Bjack795/WemosD32pro_EPD_Typewriter/Case/Cerniera/Cerniera 2.stl

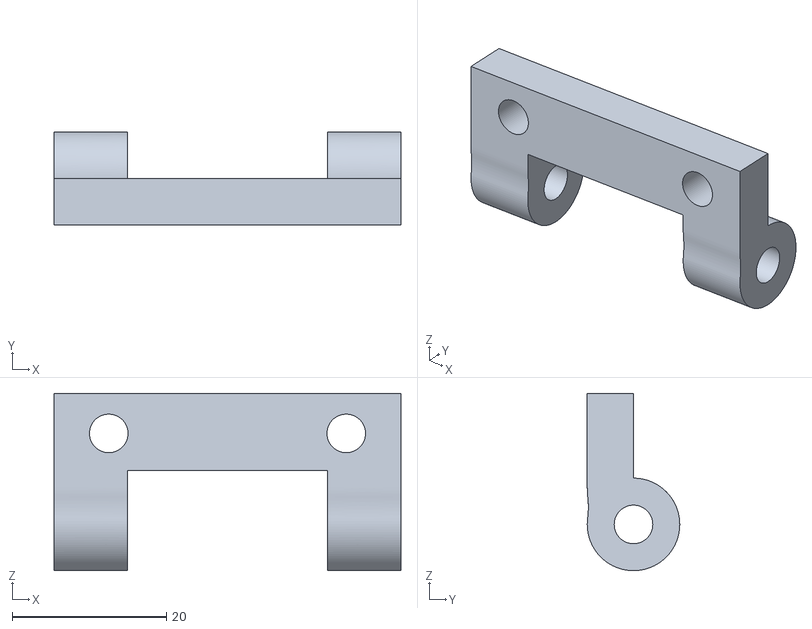
[picture p16: CAD file, 2019-07-26]
Case/Cerniera/Cerniera 2.stl
45.0 x 12.0 x 23.0
