Bjack795/WemosD32pro_EPD_Typewriter/Case/Cerniera/Definitiva/Cerniera_cov.stl

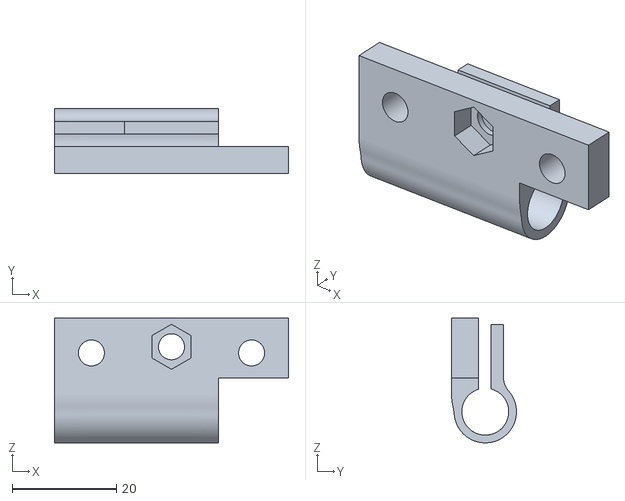
[picture p17: CAD file, 2019-07-26]
Case/Cerniera/Definitiva/Cerniera_cov.stl
45.0 x 12.5 x 24.0
