Bjack795/WemosD32pro_EPD_Typewriter/Case/Cerniera/Versione 3/Cerniera 5.5.stl

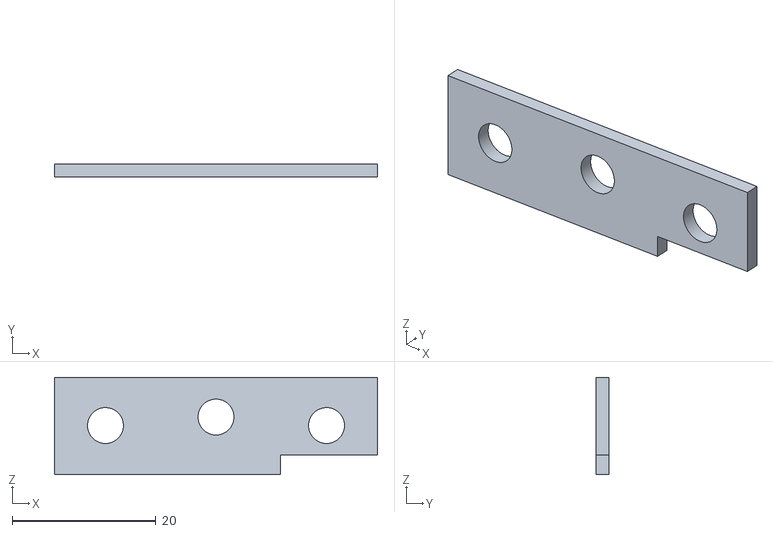
[picture p18: CAD file, 2019-07-26]
Case/Cerniera/Versione 3/Cerniera 5.5.stl
45.0 x 1.84 x 13.5
