Bjack795/WemosD32pro_EPD_Typewriter/Case/Case 3Dprinted/A/Case_A1.stl

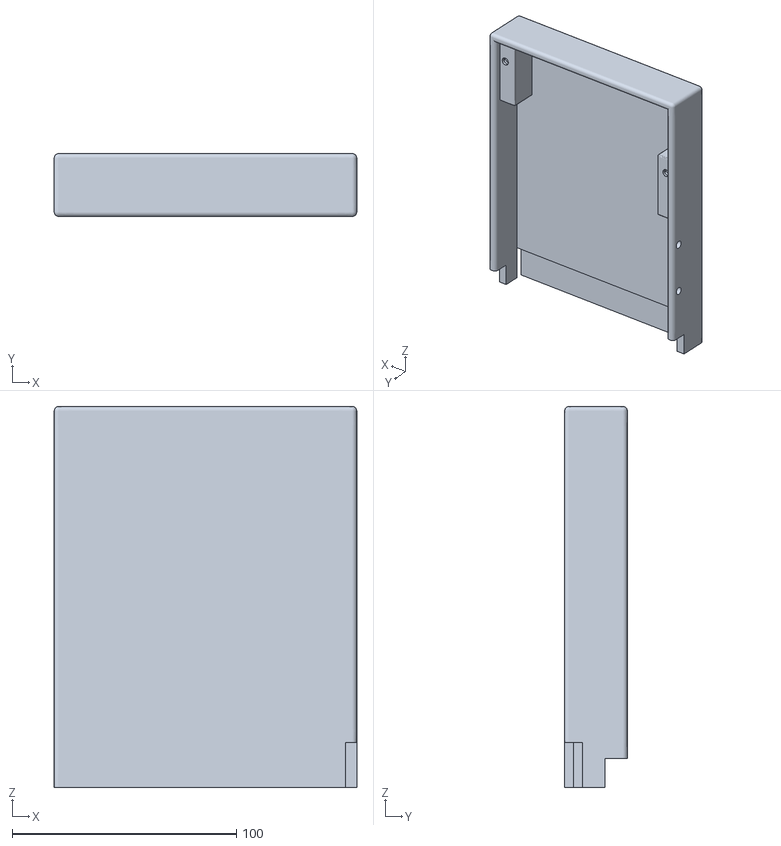
[picture p19: CAD file, 2019-07-26]
Case/Case 3Dprinted/A/Case_A1.stl
135.0 x 28.0 x 170.0
