Bjack795/WemosD32pro_EPD_Typewriter/Case/Case 3Dprinted/B/CE3_Case_B1.3mf

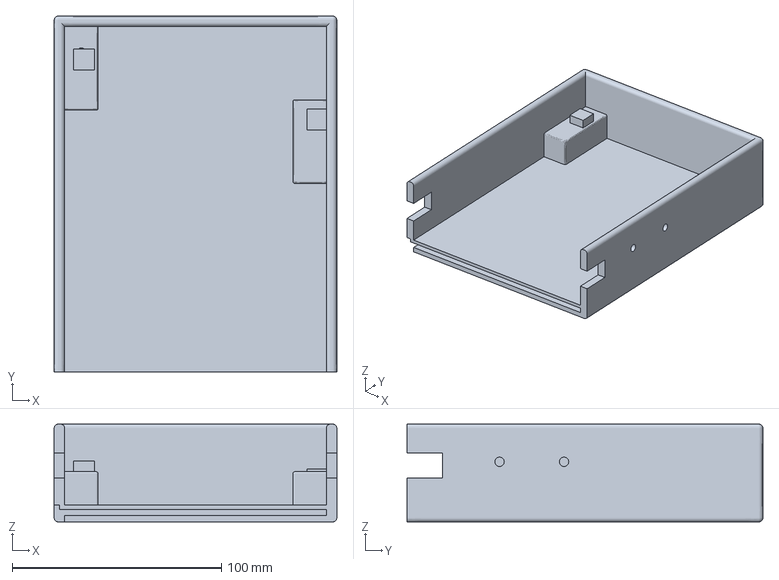
[picture p20: CAD file, 2019-07-26]
Case/Case 3Dprinted/B/CE3_Case_B1.3mf
135.0 x 170.0 x 46.7 mm
