Bjack795/WemosD32pro_EPD_Typewriter/Case/Case 3Dprinted/Placca B/PlaccaB_1.stl

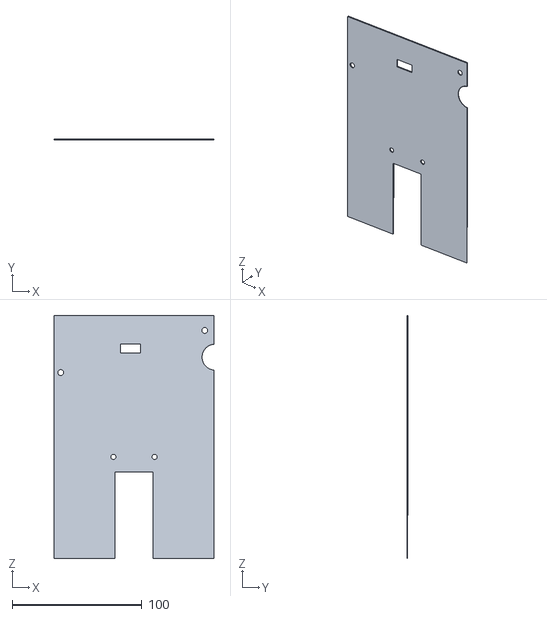
[picture p21: CAD file, 2019-08-01]
Case/Case 3Dprinted/Placca B/PlaccaB_1.stl
123.0 x 1.00 x 187.3
