Bjack795/WemosD32pro_EPD_Typewriter/Case/Case 3Dprinted/Placchetta/Placchetta.stl

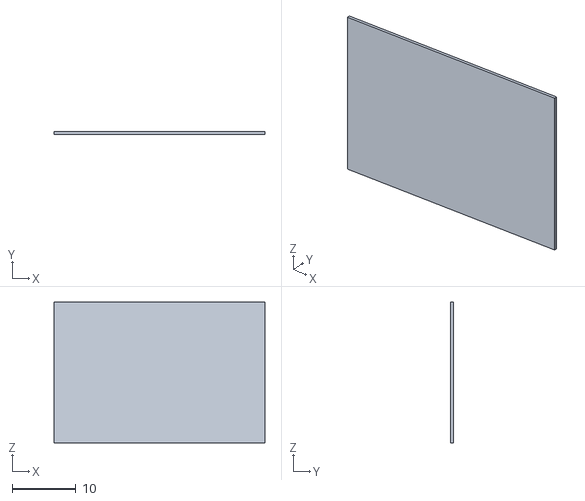
[picture p22: CAD file, 2019-08-01]
Case/Case 3Dprinted/Placchetta/Placchetta.stl
33.0 x 0.4 x 22.0
