Bjack795/WemosD32pro_EPD_Typewriter/Case/Cerniera/CE3_Cerniera.3mf

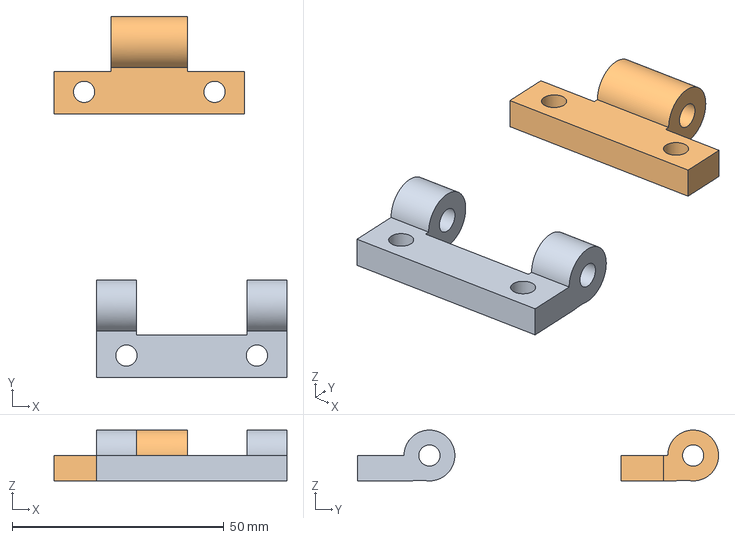
[picture p23: CAD file, 2019-07-26]
Case/Cerniera/CE3_Cerniera.3mf
55.0 x 85.2 x 12.0 mm
