Bjack795/WemosD32pro_EPD_Typewriter/Case/Cerniera/Definitiva/Cerniera_definitiva.3mf

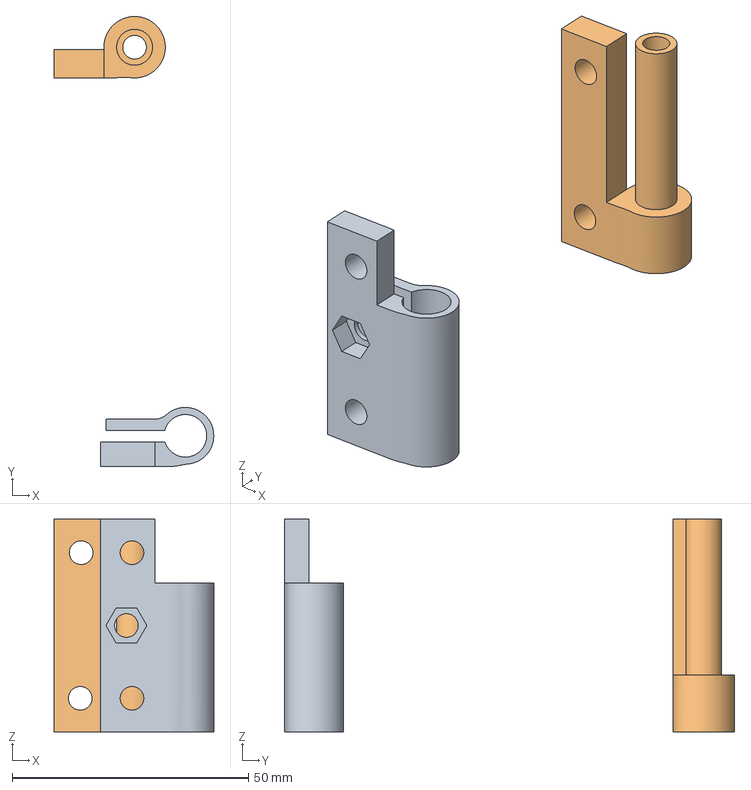
[picture p24: CAD file, 2019-07-26]
Case/Cerniera/Definitiva/Cerniera_definitiva.3mf
33.8 x 95.2 x 45.0 mm
