Bjack795/WemosD32pro_EPD_Typewriter/Case/Cerniera/Versione 3/Cerniera_Versione 3.3mf

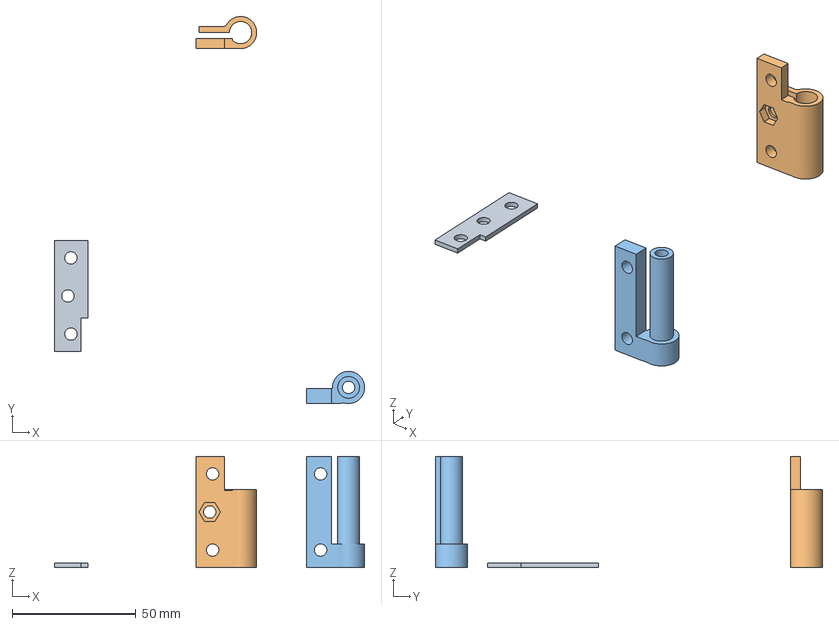
[picture p25: CAD file, 2019-07-26]
Case/Cerniera/Versione 3/Cerniera_Versione 3.3mf
125.5 x 156.5 x 45.0 mm
