Bjack795/WemosD32pro_EPD_Typewriter/Case/Case 3Dprinted/A/CE3_Case_A2.3mf

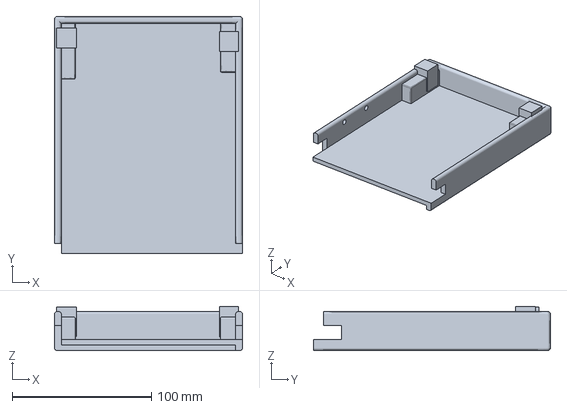
[picture p26: CAD file, 2019-07-26]
Case/Case 3Dprinted/A/CE3_Case_A2.3mf
135.0 x 170.0 x 31.6 mm
