Bjack795/WemosD32pro_EPD_Typewriter/Case/Case 3Dprinted/Prove/CE3_Prova A1.3mf

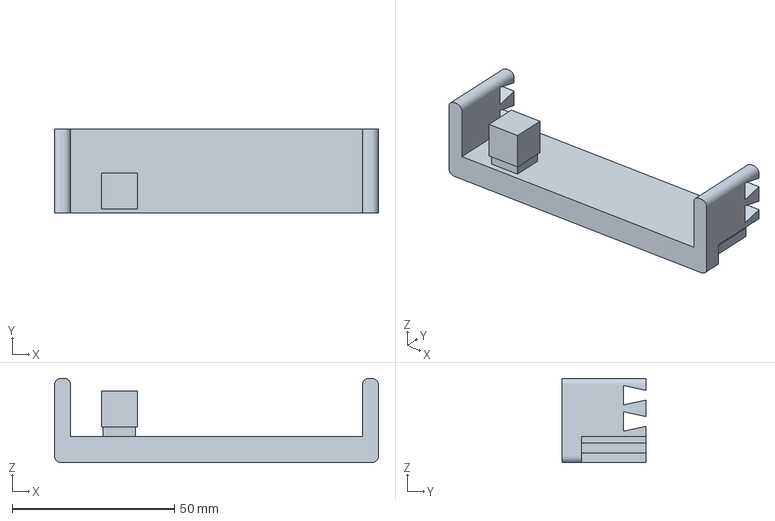
[picture p27: CAD file, 2019-07-26]
Case/Case 3Dprinted/Prove/CE3_Prova A1.3mf
100.0 x 26.0 x 26.0 mm
