Bjack795/WemosD32pro_EPD_Typewriter/Case/Cerniera/Versione 3/Cerniera 6.stl

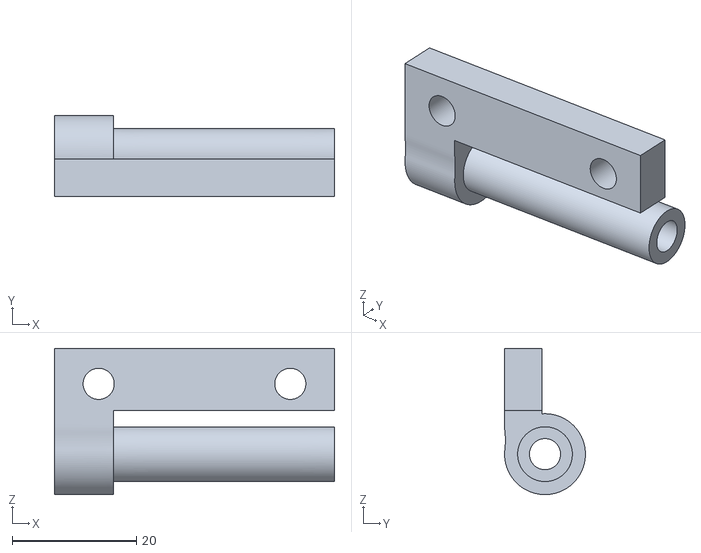
[picture p28: CAD file, 2019-07-26]
Case/Cerniera/Versione 3/Cerniera 6.stl
45.0 x 13.0 x 23.5
