Bjack795/WemosD32pro_EPD_Typewriter/Case/Case 3Dprinted/Prove/Prova dado.stl

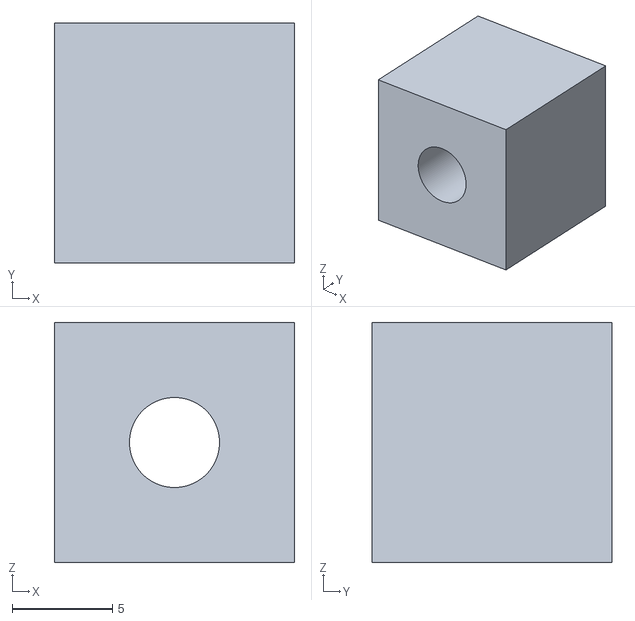
[picture p29: CAD file, 2019-07-26]
Case/Case 3Dprinted/Prove/Prova dado.stl
12.0 x 12.0 x 12.0
