Bjack795/WemosD32pro_EPD_Typewriter/Case/Cerniera/Cerniera 3.stl

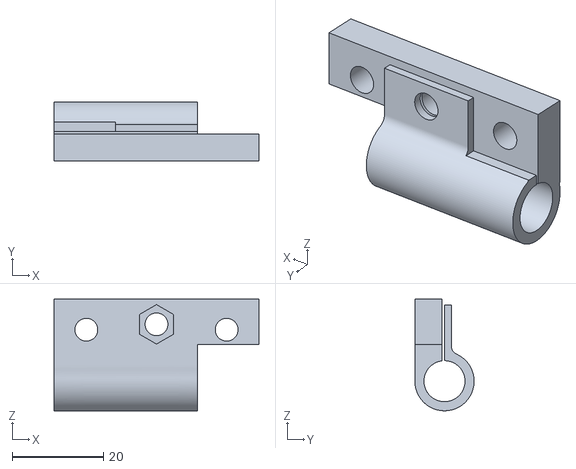
[picture p30: CAD file, 2019-07-26]
Case/Cerniera/Cerniera 3.stl
45.0 x 13.0 x 24.5
