Bjack795/WemosD32pro_EPD_Typewriter/Case/Case 3Dprinted/Prove/CE3_Prova supporti.3mf

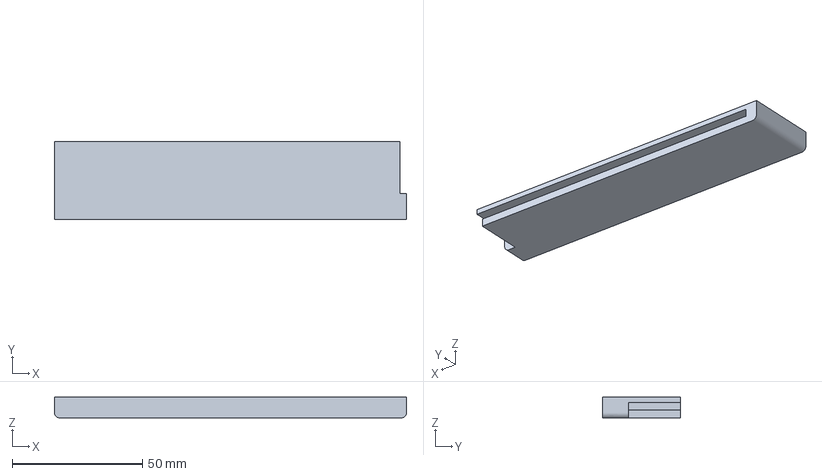
[picture p31: CAD file, 2019-07-26]
Case/Case 3Dprinted/Prove/CE3_Prova supporti.3mf
135.0 x 30.0 x 8.00 mm
