Bjack795/WemosD32pro_EPD_Typewriter/Case/Cerniera/Cerniera 1.stl

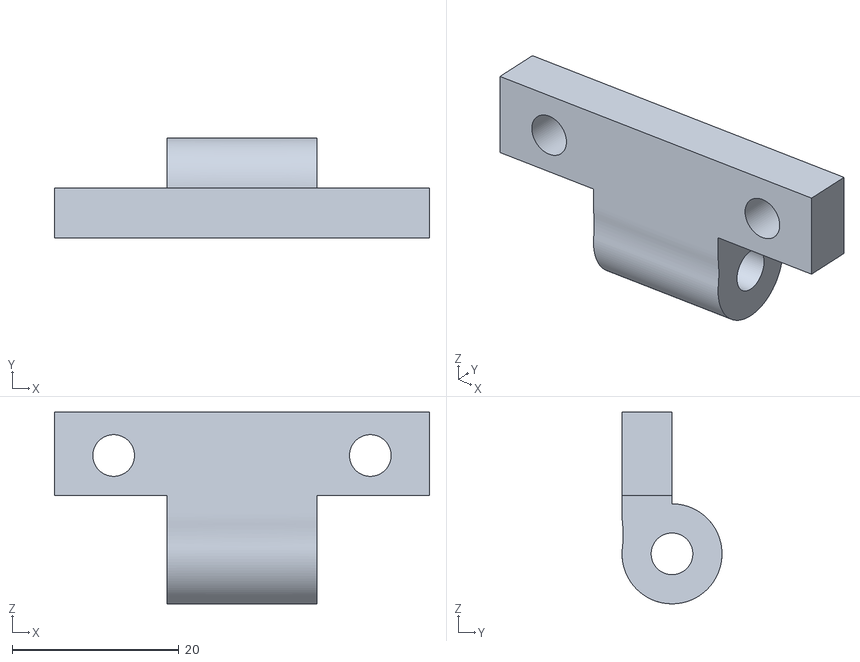
[picture p32: CAD file, 2019-07-26]
Case/Cerniera/Cerniera 1.stl
45.0 x 12.0 x 23.0
