Bjack795/WemosD32pro_EPD_Typewriter/Case/Case 3Dprinted/Prove/CE3_Prova_A2.3mf

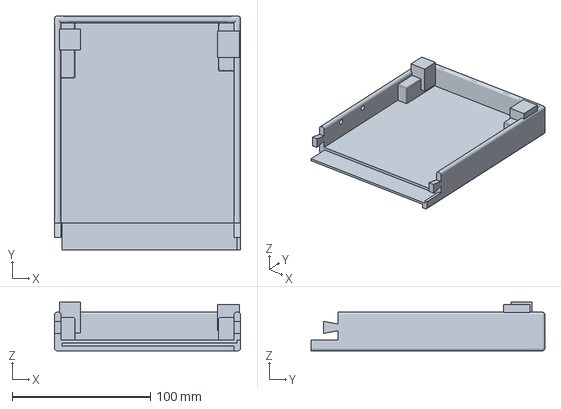
[picture p33: CAD file, 2019-07-26]
Case/Case 3Dprinted/Prove/CE3_Prova_A2.3mf
135.0 x 169.5 x 35.2 mm
