Bjack795/WemosD32pro_EPD_Typewriter/Case/Case 3Dprinted/Prove/incastri 2.stl

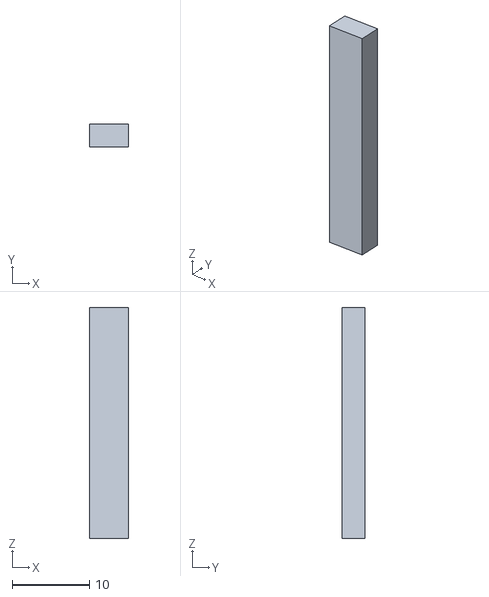
[picture p34: CAD file, 2019-07-26]
Case/Case 3Dprinted/Prove/incastri 2.stl
5.00 x 3.00 x 30.0
