Bjack795/WemosD32pro_EPD_Typewriter/TYPEWRITER_EPD/Webserver_functions.ino

//Webserver_functions.ino

/*  Version 1
 *  ESP32/ESP8266 example of downloading, uploading, deleting, streaming and a file directory of a device's Filing System

 This software, the ideas and concepts is Copyright (c) David Bird 2018. All rights to this software are reserved.
 
 Any redistribution or reproduction of any part or all of the contents in any form is prohibited other than the following:
 1. You may print or download to a local hard disk extracts for your personal and non-commercial use only.
 2. You may copy the content to individual third parties for their personal use, but only if you acknowledge the author David Bird as the source of the material.
 3. You may not, except with my express written permission, distribute or commercially exploit the content.
 4. You may not transmit it or store it in any other website or other form of electronic retrieval system for commercial purposes.

 The above copyright ('as annotated') notice and this permission notice shall be included in all copies or substantial portions of the Software and where the
 software use is visible to an end-user.
 
 THE SOFTWARE IS PROVIDED "AS IS" FOR PRIVATE USE ONLY, IT IS NOT FOR COMMERCIAL USE IN WHOLE OR PART OR CONCEPT. FOR PERSONAL USE IT IS SUPPLIED WITHOUT WARRANTY 
 OF ANY KIND, EXPRESS OR IMPLIED, INCLUDING BUT NOT LIMITED TO THE WARRANTIES OF MERCHANTABILITY, FITNESS FOR A PARTICULAR PURPOSE AND NONINFRINGEMENT.
 IN NO EVENT SHALL THE AUTHOR OR COPYRIGHT HOLDER BE LIABLE FOR ANY CLAIM, DAMAGES OR OTHER LIABILITY, WHETHER IN AN ACTION OF CONTRACT, TORT OR OTHERWISE, ARISING 
 FROM, OUT OF OR IN CONNECTION WITH THE SOFTWARE OR THE USE OR OTHER DEALINGS IN THE SOFTWARE.
 See more at http://www.dsbird.org.uk */
 
void Webserver_connect(int timeout)
{
  wm.setEnableConfigPortal(false);
  wm.setConfigPortalTimeout(timeout);

  if(OK_SERVER == true)
  {
    server.stop();
    OK_SERVER = false;
  }
  
  // IP for wifimanager:      192.168.4.1
    if(!wm.autoConnect(SERVER_NAME)) 
    {
        Serial.println("Failed to connect");
        OK_WIFI = false;
        // ESP.restart();
    } 
    else {
        //if you get here you have connected to the WiFi   
        OK_WIFI = true; 
        Serial.println("connected...yeey :)");
        Serial.print("LocalIP :");
        Serial.println(WiFi.localIP());
        Serial.print("Gateway :");
        Serial.println(WiFi.gatewayIP());
        Serial.print("Subnet :");
        Serial.println(WiFi.subnetMask());
        Serial.print("SSID :");
        Serial.println(WiFi.SSID());
        Serial.println("\nConnected to "+WiFi.SSID()+" Use IP address: "+WiFi.localIP().toString()); // Report which SSID and IP is in use
        CONNECTED_WIFI = WiFi.SSID();
        PASSPORT_IP = WiFi.localIP().toString();
        Serial.println();
        Serial.println("THE WEBSERVER IS ON THIS IP:");
        Serial.println(WiFi.localIP());
        Serial.println();
        Serial.println();

        Serverfun();
  }

    //Serverfun();
 

}
////////////////////////***************************************************************************
void Webserver_autoconnect(int timeout)
{
  wm.setEnableConfigPortal(true);
  wm.setConfigPortalTimeout(timeout);

  if(OK_SERVER == true)
  {
    server.stop();
    OK_SERVER = false;
  }
  
  // IP for wifimanager:      192.168.4.1
    if(!wm.autoConnect(SERVER_NAME)) 
    {
        Serial.println("Failed to connect");
        OK_WIFI = false;
        // ESP.restart();
    } 
    else {
        //if you get here you have connected to the WiFi   
        OK_WIFI = true; 
        Serial.println("connected...yeey :)");
        Serial.print("LocalIP :");
        Serial.println(WiFi.localIP());
        Serial.print("Gateway :");
        Serial.println(WiFi.gatewayIP());
        Serial.print("Subnet :");
        Serial.println(WiFi.subnetMask());
        Serial.print("SSID :");
        Serial.println(WiFi.SSID());
        Serial.println("\nConnected to "+WiFi.SSID()+" Use IP address: "+WiFi.localIP().toString()); // Report which SSID and IP is in use
        CONNECTED_WIFI = WiFi.SSID();
        PASSPORT_IP = WiFi.localIP().toString();
        Serial.println();
        Serial.println("THE WEBSERVER IS ON THIS IP:");
        Serial.println(WiFi.localIP());
        Serial.println();
        Serial.println();

        Serverfun();
  }

    //Serverfun();
 

}
//~~~~~~~~~~~~~~~~~~~~~~~~~~~~~~~~~~~~~~~~~~~~~~~~~~~~~~~~~~~~~~~~~~~~~~~~~~~
void Webserver_portal(int timeout)
{
  
    display.setTextColor(GxEPD_BLACK);
    display.setFullWindow();
    display.fillScreen(GxEPD_WHITE);

  // IP for wifimanager:      192.168.4.1
    if(!wm.startConfigPortal(SERVER_NAME))  //WiFi.softAPIP()
    {
        Serial.println("Failed to connect");
        OK_WIFI = false;

      
      display.setCursor(MARGINE_SX,0*(INGOMBRO+INTERLINEA)+ MARGINE_UP);
      display.print("Failed to connect");
        
    } 
    else 
    {
        //if you get here you have connected to the WiFi   
      OK_WIFI = true; 
      display.setCursor(MARGINE_SX,0*(INGOMBRO+INTERLINEA)+ MARGINE_UP);
      display.print("Connected");
      
      Serial.println("connected...yeey :)");
      Serial.print("LocalIP :");
      Serial.println(WiFi.localIP());
      Serial.print("Gateway :");
      Serial.println(WiFi.gatewayIP());
      Serial.print("Subnet :");
      Serial.println(WiFi.subnetMask());
      Serial.print("SSID :");
      Serial.println(WiFi.SSID());
      Serial.println("\nConnected to "+WiFi.SSID()+" Use IP address: "+WiFi.localIP().toString()); // Report which SSID and IP is in use
      CONNECTED_WIFI = WiFi.SSID();
      PASSPORT_IP = WiFi.localIP().toString();
      Serial.println();
      Serial.println("THE WEBSERVER IS ON THIS IP:");
      Serial.println(WiFi.localIP());
      Serial.println();
      Serial.println();

      Serverfun(); 
  }
  display.setCursor(MARGINE_SX,2*(INGOMBRO+INTERLINEA)+ MARGINE_UP);
  display.print("Restarting...");
  display.display(true);
  delay(1000);
  ESP.restart();


}

/////////////////////////////***********************************************************************************************************
void Serverfun()
{
    // The logical name http://fileserver.local will also access the device if you have 'Bonjour' running or your system supports multicast dns
  if (!MDNS.begin(servername)) {          // Set your preferred server name, if you use "myserver" the address would be http://myserver.local/
    Serial.println(F("Error setting up MDNS responder!")); 
    ESP.restart(); 
  } 
  
  ///////////////////////////// Server Commands 
  server.on("/",         HomePage);
  server.on("/download", File_Download);
  server.on("/upload",   File_Upload);
  server.on("/fupload",  HTTP_POST,[](){ server.send(200);}, handleFileUpload);
  server.on("/stream",   File_Stream);
  server.on("/delete",   File_Delete);
  server.on("/dir",      SD_dir);
  
  ///////////////////////////// End of Request commands
  server.begin();
  Serial.println("HTTP server started GINOPINO");
  OK_SERVER = true;
}

///////////////////////////////////////*********************************************************************
void Webserver_loop(void)
{
  if (OK_SERVER == true)
  {
    server.handleClient(); // Listen for client connections
  }
  
  
}

//////////////////////////////////////////
void Webserver_reset()
{
  wm.resetSettings();
  ESP.restart();
}

// All supporting functions from here...
//~~~~~~~~~~~~~~~~~~~~~~~~~~~~~~~~~~~~~~~~~~~~~~~~~~~~~~~~~~~~~~~~~~~~~~~~~~~
void HomePage(){
  SendHTML_Header();
  webpage += F("<a href='/download'><button>Download</button></a>");
  webpage += F("<a href='/upload'><button>Upload</button></a>");
  webpage += F("<a href='/stream'><button>Stream</button></a>");
  webpage += F("<a href='/delete'><button>Delete</button></a>");
  webpage += F("<a href='/dir'><button>Directory</button></a>");
  append_page_footer();
  SendHTML_Content();
  SendHTML_Stop(); // Stop is needed because no content length was sent
}
//~~~~~~~~~~~~~~~~~~~~~~~~~~~~~~~~~~~~~~~~~~~~~~~~~~~~~~~~~~~~~~~~~~~~~~~~~~~
void File_Download(){ // This gets called twice, the first pass selects the input, the second pass then processes the command line arguments
  if (server.args() > 0 ) { // Arguments were received
    if (server.hasArg("download")) SD_file_download(server.arg(0));
  }
  else SelectInput("Enter filename to download","download","download");
}
//~~~~~~~~~~~~~~~~~~~~~~~~~~~~~~~~~~~~~~~~~~~~~~~~~~~~~~~~~~~~~~~~~~~~~~~~~~~
void SD_file_download(String filename){
  if (SD_present) { 
    File download = SD.open("/"+filename);
    if (download) {
      server.sendHeader("Content-Type", "text/text");
      server.sendHeader("Content-Disposition", "attachment; filename="+filename);
      server.sendHeader("Connection", "close");
      server.streamFile(download, "application/octet-stream");
      download.close();
    } else ReportFileNotPresent("download"); 
  } else ReportSDNotPresent();
}
//~~~~~~~~~~~~~~~~~~~~~~~~~~~~~~~~~~~~~~~~~~~~~~~~~~~~~~~~~~~~~~~~~~~~~~~~~~~
void File_Upload(){
  append_page_header();
  webpage += F("<h3>Select File to Upload</h3>"); 
  webpage += F("<FORM action='/fupload' method='post' enctype='multipart/form-data'>");
  webpage += F("<input class='buttons' style='width:40%' type='file' name='fupload' id = 'fupload' value=''><br>");
  webpage += F("<br><button class='buttons' style='width:10%' type='submit'>Upload File</button><br>");
  webpage += F("<a href='/'>[Back]</a><br><br>");
  append_page_footer();
  server.send(200, "text/html",webpage);
}
//~~~~~~~~~~~~~~~~~~~~~~~~~~~~~~~~~~~~~~~~~~~~~~~~~~~~~~~~~~~~~~~~~~~~~~~~~~~
File UploadFile; 
void handleFileUpload(){ // upload a new file to the Filing system
  HTTPUpload& uploadfile = server.upload(); // See https://github.com/esp8266/Arduino/tree/master/libraries/ESP8266WebServer/srcv
                                            // For further information on 'status' structure, there are other reasons such as a failed transfer that could be used
  if(uploadfile.status == UPLOAD_FILE_START)
  {
    String filename = uploadfile.filename;
    for(int aa = 0; aa<filename.length();aa++)
      {
        if(filename[aa]== '=')//put the equal instead of /
        {
          filename[aa] = '/';
        }
      }
      Serial.println(filename);
    if(!filename.startsWith("/")) 
    {
      filename = "/"+filename;
    }
    Serial.print("Upload File Name: "); Serial.println(filename);
    SD.remove(filename);                         // Remove a previous version, otherwise data is appended the file again
    UploadFile = SD.open(filename, FILE_WRITE);  // Open the file for writing in SPIFFS (create it, if doesn't exist)
    filename = String();
  }
  else if (uploadfile.status == UPLOAD_FILE_WRITE)
  {
    if(UploadFile) UploadFile.write(uploadfile.buf, uploadfile.currentSize); // Write the received bytes to the file
  } 
  else if (uploadfile.status == UPLOAD_FILE_END)
  {
    if(UploadFile)          // If the file was successfully created
    {                                    
      UploadFile.close();   // Close the file again
      Serial.print("Upload Size: "); Serial.println(uploadfile.totalSize);
      webpage = "";
      append_page_header();
      webpage += F("<h3>File was successfully uploaded</h3>"); 
      webpage += F("<h2>Uploaded File Name: "); webpage += uploadfile.filename+"</h2>";
      webpage += F("<h2>File Size: "); webpage += file_size(uploadfile.totalSize) + "</h2><br>"; 
      append_page_footer();
      server.send(200,"text/html",webpage);
    } 
    else
    {
      ReportCouldNotCreateFile("upload");
    }
  }
}
//~~~~~~~~~~~~~~~~~~~~~~~~~~~~~~~~~~~~~~~~~~~~~~~~~~~~~~~~~~~~~~~~~~~~~~~~~~~
void SD_dir(){
  if (SD_present) { 
    File root = SD.open("/");
    if (root) {
      root.rewindDirectory();
      SendHTML_Header();
      webpage += F("<h3 class='rcorners_m'>SD Card Contents</h3><br>");
      webpage += F("<table align='center'>");
      webpage += F("<tr><th>Name/Type</th><th style='width:20%'>Type File/Dir</th><th>File Size</th></tr>");
      printDirectory("/",0);
      webpage += F("</table>");
      SendHTML_Content();
      root.close();
    }
    else 
    {
      SendHTML_Header();
      webpage += F("<h3>No Files Found</h3>");
    }
    append_page_footer();
    SendHTML_Content();
    SendHTML_Stop();   // Stop is needed because no content length was sent
  } else ReportSDNotPresent();
}
//~~~~~~~~~~~~~~~~~~~~~~~~~~~~~~~~~~~~~~~~~~~~~~~~~~~~~~~~~~~~~~~~~~~~~~~~~~~
void printDirectory(const char * dirname, uint8_t LEVELs){
  File root = SD.open(dirname);
  #ifdef ESP8266
  root.rewindDirectory(); //Only needed for ESP8266
  #endif
  if(!root){
    return;
  }
  if(!root.isDirectory()){
    return;
  }
  File file = root.openNextFile();
  while(file){
    if (webpage.length() > 1000) {
      SendHTML_Content();
    }
    if(file.isDirectory()){
      webpage += "<tr><td>"+String(file.isDirectory()?"Dir":"File")+"</td><td>"+String(file.name())+"</td><td></td></tr>";
      printDirectory(file.name(), LEVELs-1);
    }
    else
    {
      webpage += "<tr><td>"+String(file.name())+"</td>";
      webpage += "<td>"+String(file.isDirectory()?"Dir":"File")+"</td>";
      int bytes = file.size();
      String fsize = "";
      if (bytes < 1024)                     fsize = String(bytes)+" B";
      else if(bytes < (1024 * 1024))        fsize = String(bytes/1024.0,3)+" KB";
      else if(bytes < (1024 * 1024 * 1024)) fsize = String(bytes/1024.0/1024.0,3)+" MB";
      else                                  fsize = String(bytes/1024.0/1024.0/1024.0,3)+" GB";
      webpage += "<td>"+fsize+"</td></tr>";
    }
    file = root.openNextFile();
  }
  file.close();
}
//~~~~~~~~~~~~~~~~~~~~~~~~~~~~~~~~~~~~~~~~~~~~~~~~~~~~~~~~~~~~~~~~~~~~~~~~~~~
void File_Stream(){
  if (server.args() > 0 ) { // Arguments were received
    if (server.hasArg("stream")) SD_file_stream(server.arg(0));
  }
  else SelectInput("Enter a File to Stream","stream","stream");
}
//~~~~~~~~~~~~~~~~~~~~~~~~~~~~~~~~~~~~~~~~~~~~~~~~~~~~~~~~~~~~~~~~~~~~~~~~~~~
void SD_file_stream(String filename) { 
  if (SD_present) { 
    File dataFile = SD.open("/"+filename, FILE_READ); // Now read data from SD Card 
    if (dataFile) { 
      if (dataFile.available()) { // If data is available and present 
        String dataType = "application/octet-stream"; 
        if (server.streamFile(dataFile, dataType) != dataFile.size()) {Serial.print(F("Sent less data than expected!")); } 
      }
      dataFile.close(); // close the file: 
    } else ReportFileNotPresent("Cstream");
  } else ReportSDNotPresent(); 
}   
//~~~~~~~~~~~~~~~~~~~~~~~~~~~~~~~~~~~~~~~~~~~~~~~~~~~~~~~~~~~~~~~~~~~~~~~~~~~
void File_Delete(){
  if (server.args() > 0 ) { // Arguments were received
    if (server.hasArg("delete")) SD_file_delete(server.arg(0));
  }
  else SelectInput("Select a File to Delete","delete","delete");
}
//~~~~~~~~~~~~~~~~~~~~~~~~~~~~~~~~~~~~~~~~~~~~~~~~~~~~~~~~~~~~~~~~~~~~~~~~~~~
void SD_file_delete(String filename) { // Delete the file 
  if (SD_present) { 
    SendHTML_Header();
    File dataFile = SD.open("/"+filename, FILE_READ); // Now read data from SD Card 
    if (dataFile)
    {
      if (SD.remove("/"+filename)) {
        Serial.println(F("File deleted successfully"));
        webpage += "<h3>File '"+filename+"' has been erased</h3>"; 
        webpage += F("<a href='/delete'>[Back]</a><br><br>");
      }
      else
      { 
        webpage += F("<h3>File was not deleted - error</h3>");
        webpage += F("<a href='delete'>[Back]</a><br><br>");
      }
    } else ReportFileNotPresent("delete");
    append_page_footer(); 
    SendHTML_Content();
    SendHTML_Stop();
  } else ReportSDNotPresent();
} 
//~~~~~~~~~~~~~~~~~~~~~~~~~~~~~~~~~~~~~~~~~~~~~~~~~~~~~~~~~~~~~~~~~~~~~~~~~~~
void SendHTML_Header(){
  server.sendHeader("Cache-Control", "no-cache, no-store, must-revalidate"); 
  server.sendHeader("Pragma", "no-cache"); 
  server.sendHeader("Expires", "-1"); 
  server.setContentLength(CONTENT_LENGTH_UNKNOWN); 
  server.send(200, "text/html", ""); // Empty content inhibits Content-length header so we have to close the socket ourselves. 
  append_page_header();
  server.sendContent(webpage);
  webpage = "";
}
//~~~~~~~~~~~~~~~~~~~~~~~~~~~~~~~~~~~~~~~~~~~~~~~~~~~~~~~~~~~~~~~~~~~~~~~~~~~
void SendHTML_Content(){
  server.sendContent(webpage);
  webpage = "";
}
//~~~~~~~~~~~~~~~~~~~~~~~~~~~~~~~~~~~~~~~~~~~~~~~~~~~~~~~~~~~~~~~~~~~~~~~~~~~
void SendHTML_Stop(){
  server.sendContent("");
  server.client().stop(); // Stop is needed because no content length was sent
}
//~~~~~~~~~~~~~~~~~~~~~~~~~~~~~~~~~~~~~~~~~~~~~~~~~~~~~~~~~~~~~~~~~~~~~~~~~~~
void SelectInput(String heading1, String command, String arg_calling_name){
  SendHTML_Header();
  webpage += F("<h3>"); webpage += heading1 + "</h3>"; 
  webpage += F("<FORM action='/"); webpage += command + "' method='post'>"; // Must match the calling argument e.g. '/chart' calls '/chart' after selection but with arguments!
  webpage += F("<input type='text' name='"); webpage += arg_calling_name; webpage += F("' value=''><br>");
  webpage += F("<type='submit' name='"); webpage += arg_calling_name; webpage += F("' value=''><br><br>");
  append_page_footer();
  SendHTML_Content();
  SendHTML_Stop();
}
//~~~~~~~~~~~~~~~~~~~~~~~~~~~~~~~~~~~~~~~~~~~~~~~~~~~~~~~~~~~~~~~~~~~~~~~~~~~
void ReportSDNotPresent(){
  SendHTML_Header();
  webpage += F("<h3>No SD Card present</h3>"); 
  webpage += F("<a href='/'>[Back]</a><br><br>");
  append_page_footer();
  SendHTML_Content();
  SendHTML_Stop();
}
//~~~~~~~~~~~~~~~~~~~~~~~~~~~~~~~~~~~~~~~~~~~~~~~~~~~~~~~~~~~~~~~~~~~~~~~~~~~
void ReportFileNotPresent(String target){
  SendHTML_Header();
  webpage += F("<h3>File does not exist</h3>"); 
  webpage += F("<a href='/"); webpage += target + "'>[Back]</a><br><br>";
  append_page_footer();
  SendHTML_Content();
  SendHTML_Stop();
}
//~~~~~~~~~~~~~~~~~~~~~~~~~~~~~~~~~~~~~~~~~~~~~~~~~~~~~~~~~~~~~~~~~~~~~~~~~~~
void ReportCouldNotCreateFile(String target){
  SendHTML_Header();
  webpage += F("<h3>Could Not Create Uploaded File (write-protected?)</h3>"); 
  webpage += F("<a href='/"); webpage += target + "'>[Back]</a><br><br>";
  append_page_footer();
  SendHTML_Content();
  SendHTML_Stop();
}
//~~~~~~~~~~~~~~~~~~~~~~~~~~~~~~~~~~~~~~~~~~~~~~~~~~~~~~~~~~~~~~~~~~~~~~~~~~~
String file_size(int bytes){
  String fsize = "";
  if (bytes < 1024)                 fsize = String(bytes)+" B";
  else if(bytes < (1024*1024))      fsize = String(bytes/1024.0,3)+" KB";
  else if(bytes < (1024*1024*1024)) fsize = String(bytes/1024.0/1024.0,3)+" MB";
  else                              fsize = String(bytes/1024.0/1024.0/1024.0,3)+" GB";
  return fsize;
}
