Bjack795/WemosD32pro_EPD_Typewriter/TYPEWRITER_EPD/DATABASE_bitmaps.h

const unsigned char SABO[] = {/* 0X01,0X01,0X28,0X01,0X80,0X00, */
0X00,0X00,0X00,0X00,0X00,0X0F,0XFF,0X80,0X02,0X38,0X0E,0X00,0XC0,0XE7,0XEF,0XC0,
0X00,0X00,0X00,0X00,0X00,0X0F,0XFF,0X00,0X03,0X9F,0XFC,0X03,0XF3,0X4F,0XE7,0XE0,
0X00,0X00,0X00,0X00,0X00,0X0F,0XFF,0X00,0X01,0XC3,0XE0,0X03,0XE7,0XFF,0XE7,0XE0,
0X00,0X00,0X00,0X00,0X00,0X1F,0XFF,0X00,0X00,0XF0,0X04,0X00,0X07,0XFF,0XE7,0XE0,
0X00,0X00,0X00,0X00,0X00,0X1F,0XFF,0X00,0X00,0XDD,0XF8,0X00,0X8F,0XFF,0XF7,0XE0,
0X00,0X00,0X00,0X00,0X00,0X1F,0XFF,0X00,0X04,0XFF,0XD0,0X07,0X1F,0XFF,0XF6,0XF0,
0X00,0X00,0X00,0X00,0X00,0X1F,0XFF,0X00,0X01,0XE1,0XD8,0X1C,0X3F,0XFF,0XF6,0XF0,
0X00,0X00,0X00,0X00,0X00,0X1F,0XFF,0X00,0X00,0X80,0X38,0X10,0X7F,0XFF,0XF6,0XF0,
0X00,0X00,0X00,0X00,0X00,0X3F,0XFF,0X00,0X04,0X08,0X18,0X04,0XFF,0XFF,0XF6,0XF0,
0X00,0X00,0X00,0X00,0X00,0X3F,0XFF,0X80,0X0E,0X7F,0X80,0X39,0XF8,0X7F,0XF4,0XF0,
0X00,0X00,0X00,0X00,0X00,0X3F,0XFF,0X80,0X0C,0XC1,0XC0,0X33,0XF0,0X1C,0XE5,0XF1,
0X00,0X00,0X00,0X00,0X00,0X3F,0XFF,0X80,0X11,0X80,0X60,0X0F,0XEC,0XC1,0XED,0XE0,
0X00,0X00,0X00,0X00,0X00,0X7B,0XFF,0XC0,0X01,0X03,0X30,0X1F,0XC8,0X33,0XCF,0XC0,
0XC0,0X00,0X00,0X00,0X00,0X73,0XFF,0XC0,0X09,0X03,0X90,0X3F,0X80,0X07,0XFF,0X8E,
0XFF,0XC0,0X00,0X00,0X00,0X67,0XFF,0XE0,0X0D,0X00,0XC0,0X3F,0X80,0X07,0XFF,0X98,
0X7F,0XE3,0XF8,0X00,0X00,0X7F,0XFF,0XE0,0X0D,0X00,0X40,0X3F,0X00,0X07,0XFF,0X00,
0X7F,0XE1,0XFF,0XFC,0X00,0XDF,0XFF,0XF0,0X01,0X80,0X08,0X3F,0X00,0X17,0XFE,0X46,
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
0X00,0X00,0X00,0X00,0X00,0X00,0X00,0X00,0X00,0X00,0X00,0X00,0X00,0X00,0X00,0X00,
0X00,0X00,0X00,0X00,0X00,0X00,0X00,0X00,0X00,0X00,0X00,0X00,0X00,0X00,0X00,0X00,
0X00,0X00,0X00,0X00,0X00,0X00,0X00,0X00,0X00,0X00,0X00,0X00,0X00,0X00,0X00,0X00,
};
