Bjack795/WemosD32pro_EPD_Typewriter/TYPEWRITER_EPD/Sys_Variables.h

// Sys_Variables.h

// -----------------------------------------------
#define   servername "fileserver"  // Set your server's logical name here e.g. if 'myserver' then address is http://myserver.local/
#define ServerVersion ""
String webpage = "";
bool   SD_present = false;

#define SD_CS_pin   4
